10to7/R-Pi_NRF24L01/hw/r-pi_nrf24l01.sch

## KiCad design hw/r-pi_nrf24l01.sch (2014-06-03)

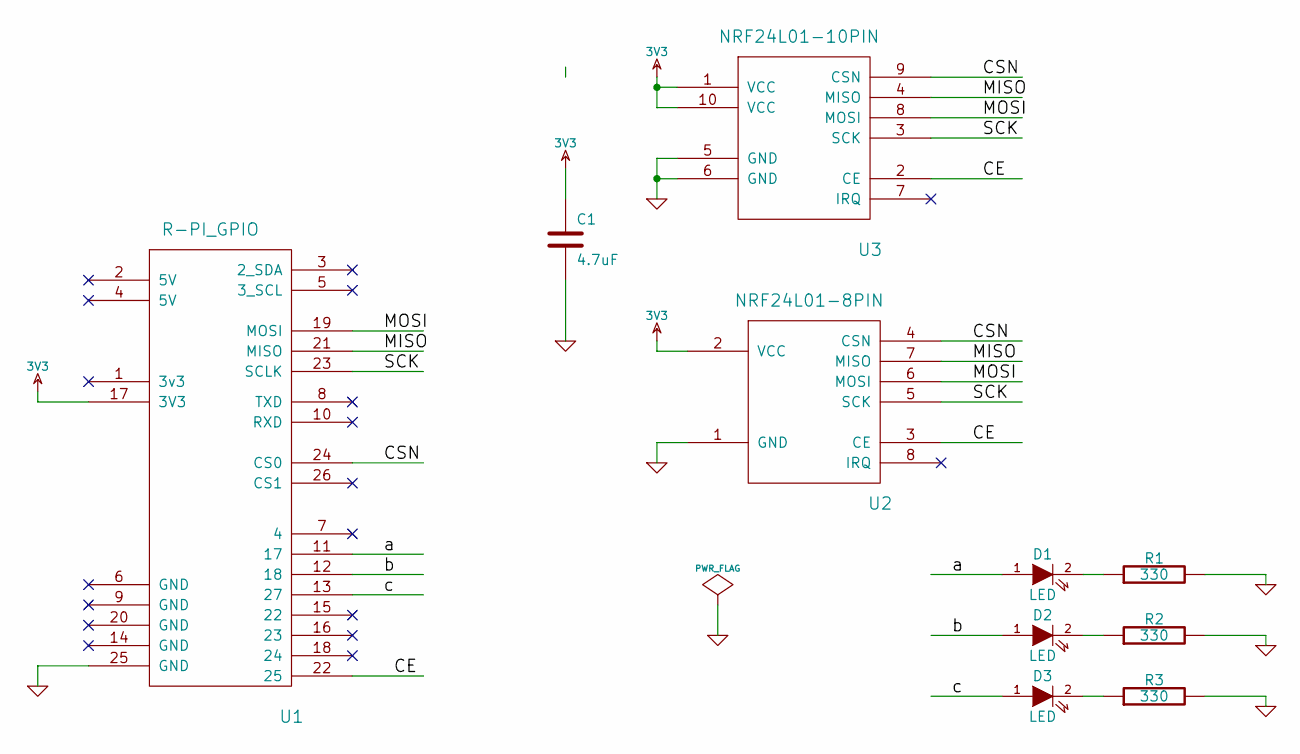
[picture p2: schematic r-pi_nrf24l01.sch]

Parts:
C1: 4.7uF
D1, D2, D3: LED
R1, R2, R3: 330
U1: R-PI_GPIO
U2: NRF24L01-8PIN
U3: NRF24L01-10PIN

Connections:
3V3: C1.1, U1.17 (3V3), U2.2 (VCC), U3.1 (VCC), U3.10 (VCC)
CE: U1.22 (25), U2.3 (CE), U3.2 (CE)
CSN: U1.24 (CS0), U2.4 (CSN), U3.9 (CSN)
GND: C1.2, R1.2, R2.2, R3.2, U1.25 (GND), U2.1 (GND), U3.5 (GND), U3.6 (GND)
MISO: U1.21 (MISO), U2.7 (MISO), U3.4 (MISO)
MOSI: U1.19 (MOSI), U2.6 (MOSI), U3.8 (MOSI)
unnamed: D1.2 (K), R1.1
unnamed: D2.2 (K), R2.1
unnamed: D3.2 (K), R3.1
SCK: U1.23 (SCLK), U2.5 (SCK), U3.3 (SCK)
a: D1.1 (A), U1.11 (17)
b: D2.1 (A), U1.12 (18)
c: D3.1 (A), U1.13 (27)
